LukasStu/Ferris-Sweep-Bling-MX-Case/gallery/case_01.jpg

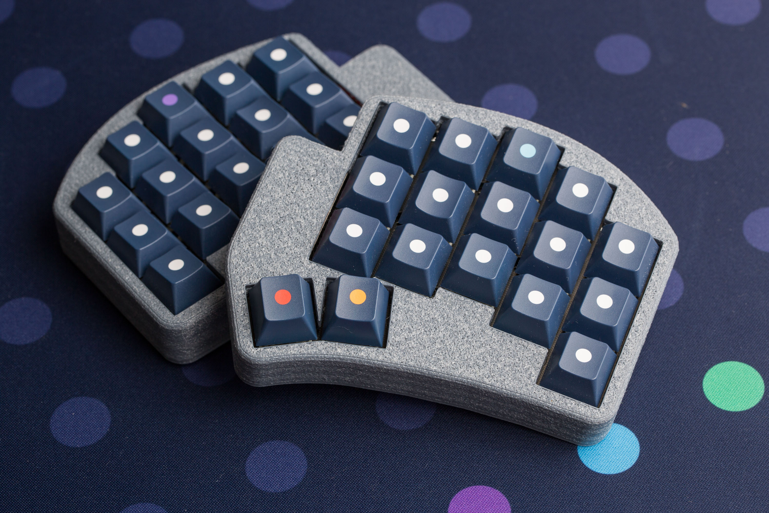
gallery/case_01.jpg
